Annex-Engineering/Carabiner-Docs/carabiner-distributor/images/Distributor_jstxh_2.png

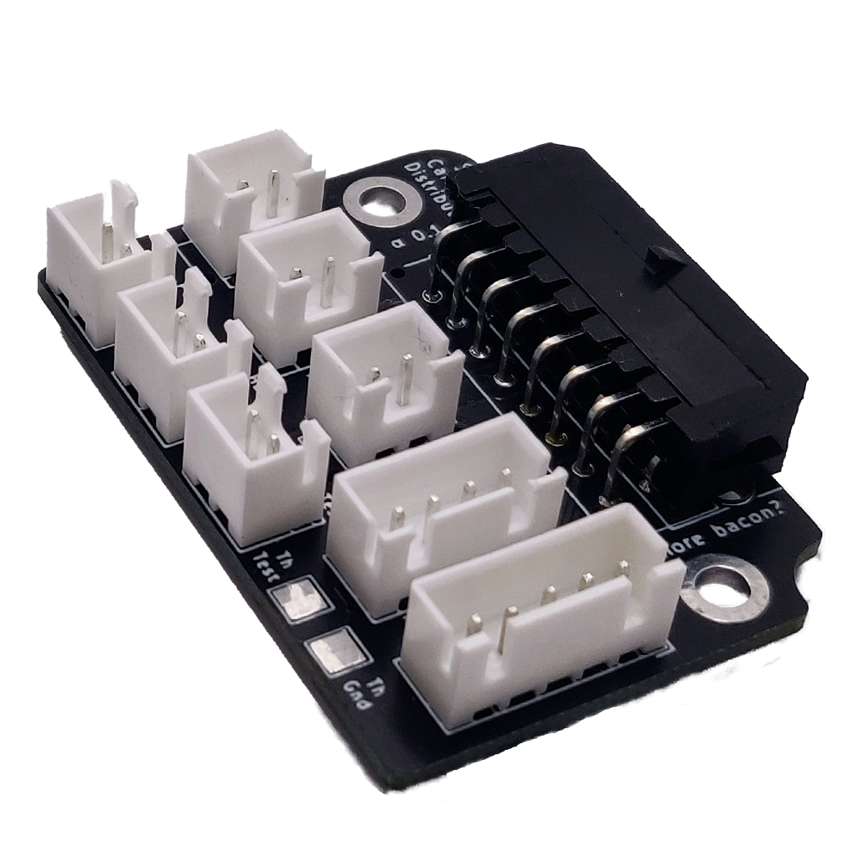
carabiner-distributor/images/Distributor_jstxh_2.png
