Annex-Engineering/Carabiner-Docs/carabiner-distributor/images/Distributor_microfit.png

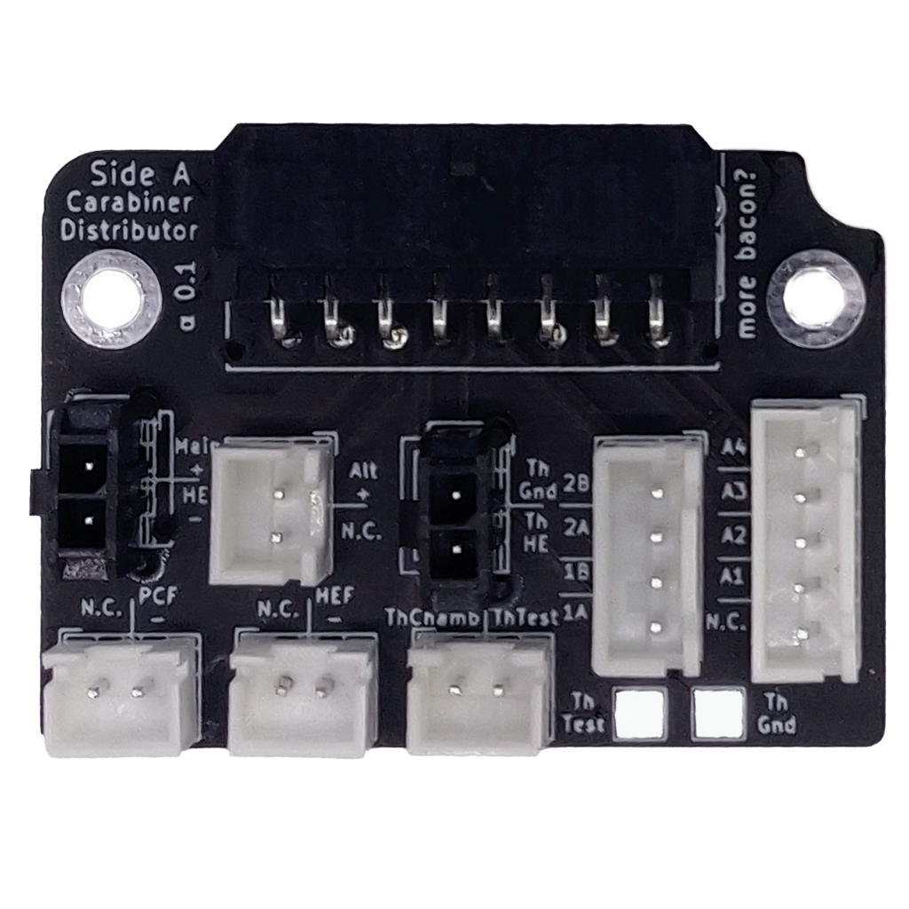
carabiner-distributor/images/Distributor_microfit.png
