Annex-Engineering/Carabiner-Docs/k3rabiner/images/Micro.jpg

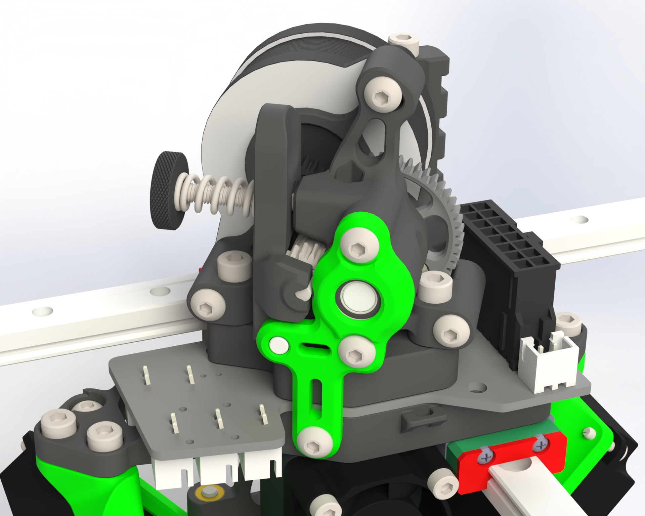
k3rabiner/images/Micro.jpg
