Annex-Engineering/Carabiner-Docs/k3rabiner/images/Mini 2.jpg

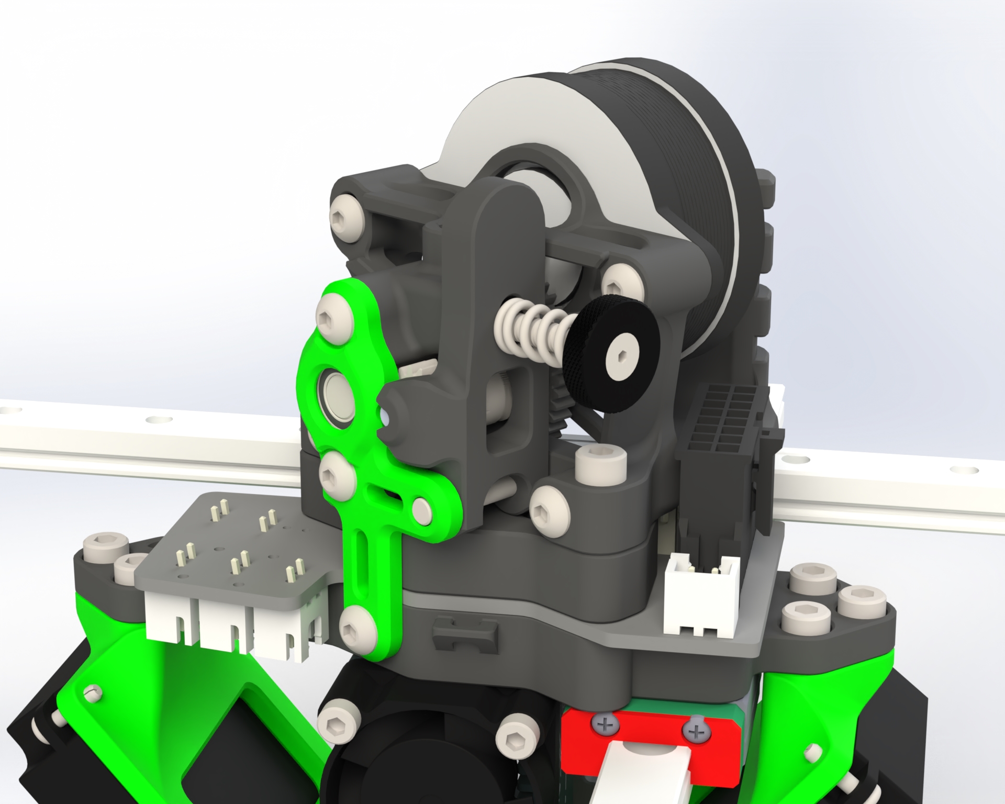
k3rabiner/images/Mini 2.jpg
