Annex-Engineering/Carabiner-Docs/k3rabiner/images/Mini.jpg

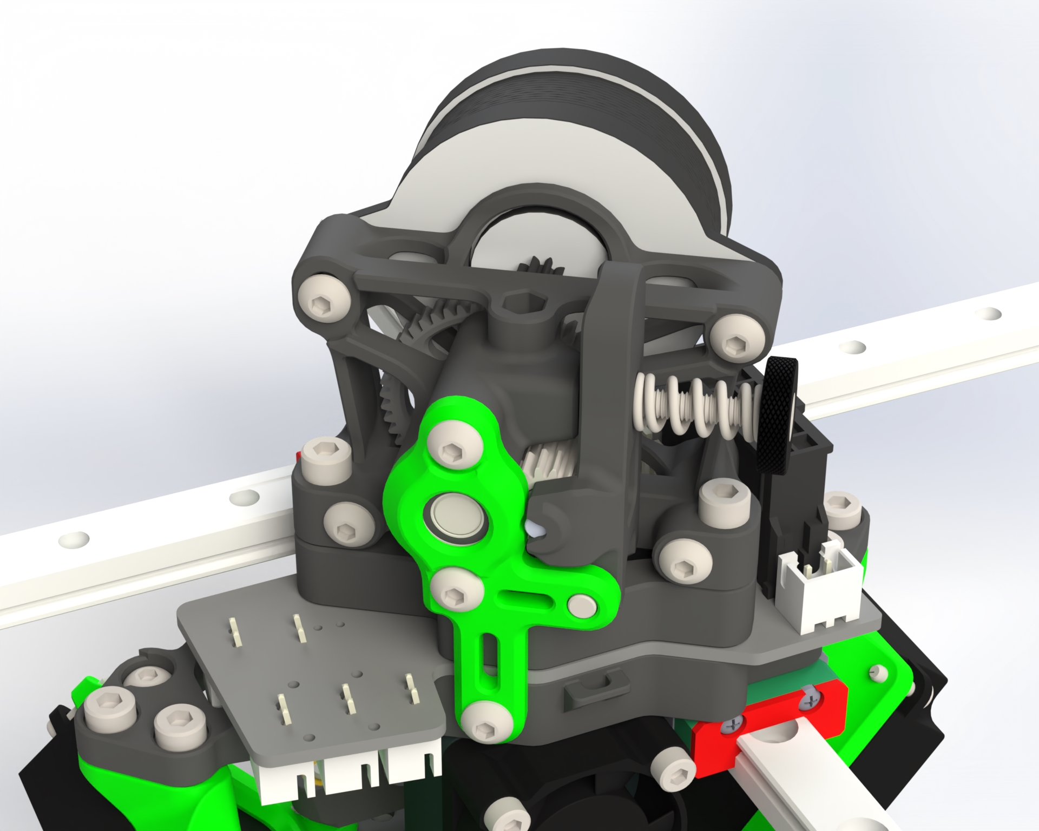
k3rabiner/images/Mini.jpg
