Annex-Engineering/Carabiner-Docs/k3rabiner/images/Untitled Project 41.jpg

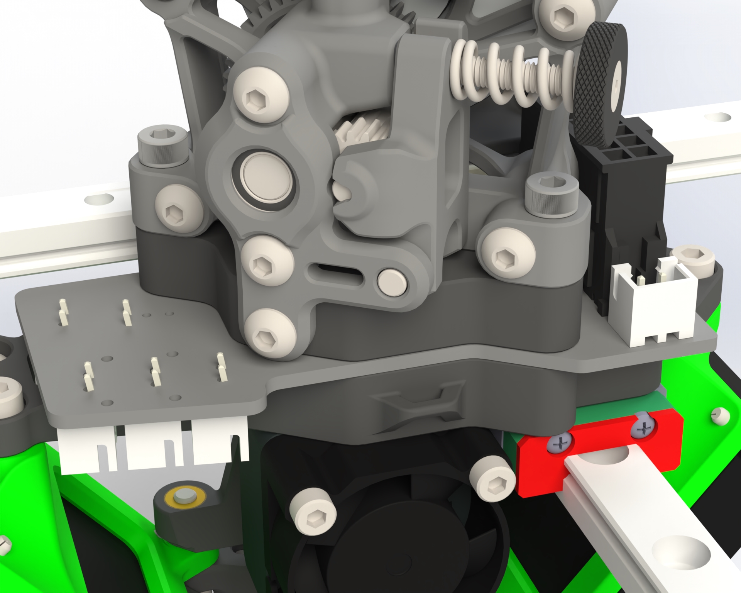
k3rabiner/images/Untitled Project 41.jpg
