Annex-Engineering/Carabiner-Docs/k3rabiner/Soldering_Jig_R1/k3rabiner-b_0_1_XH_Soldering_Jig.SLDPRT

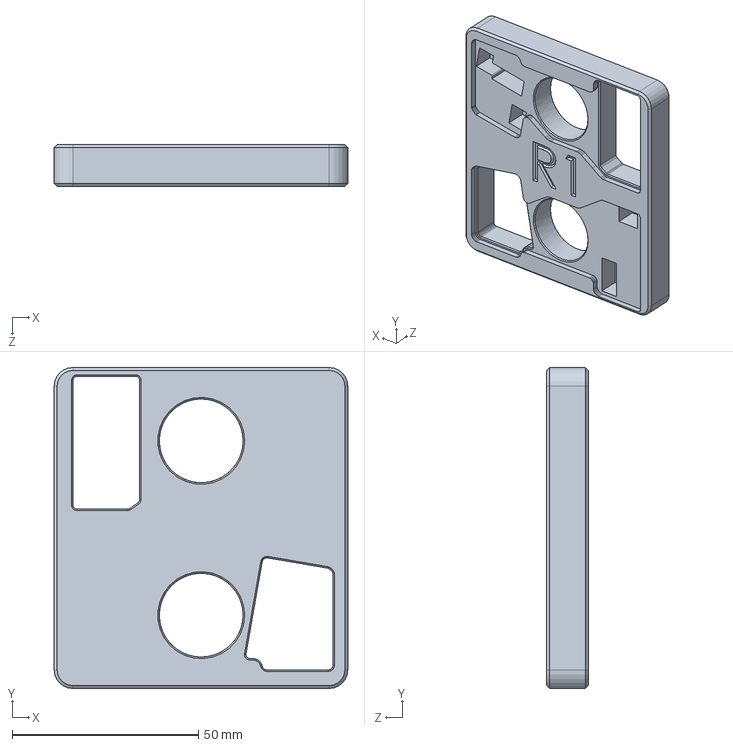
[picture p37: CAD file, 2024-07-17]
k3rabiner/Soldering_Jig_R1/k3rabiner-b_0_1_XH_Soldering_Jig.SLDPRT
78.8 x 86.1 x 11.3 mm
