Annex-Engineering/Carabiner-Docs/carabiner-classic/attachments/Afterburner/STLs/Clockwork_housing_x1_Rev1.STL

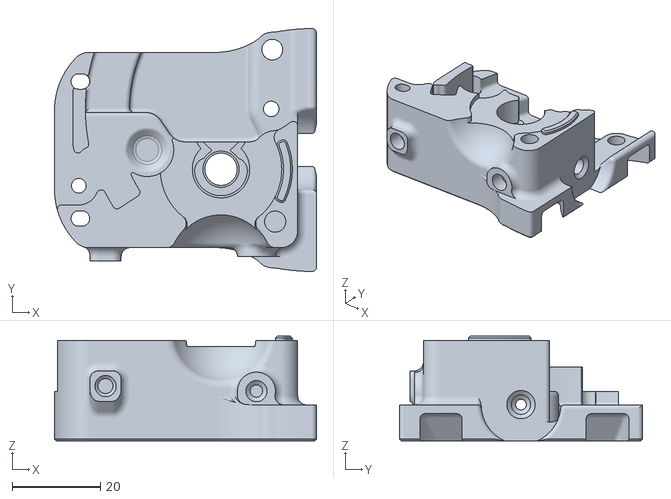
[picture p38: CAD file, 2024-07-17]
carabiner-classic/attachments/Afterburner/STLs/Clockwork_housing_x1_Rev1.STL
59.3 x 55.0 x 23.7
