Annex-Engineering/Carabiner-Docs/k3rabiner/Soldering_Jig_R1/k3rabiner-b_0_1-Jig_Bottom.SLDPRT

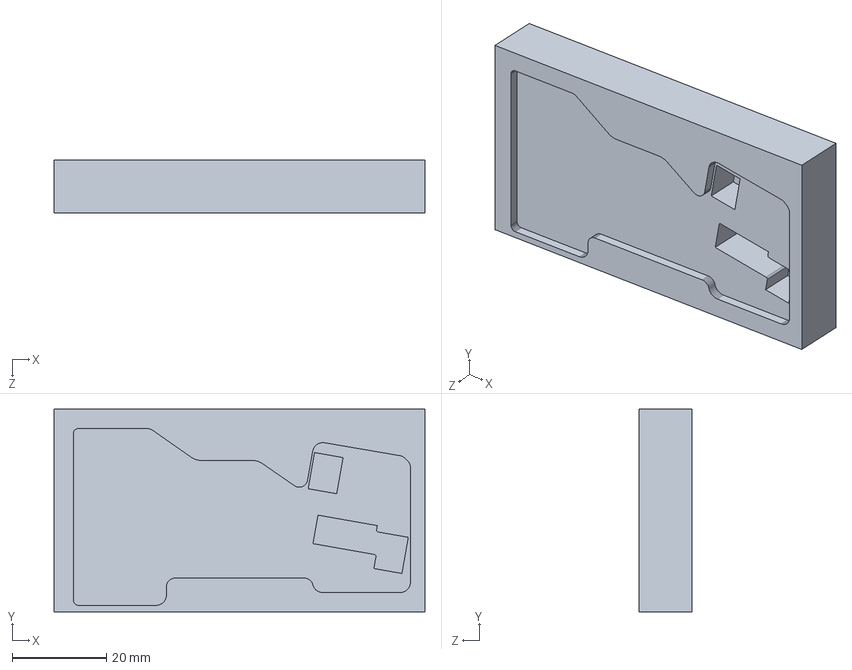
[picture p39: CAD file, 2024-07-17]
k3rabiner/Soldering_Jig_R1/k3rabiner-b_0_1-Jig_Bottom.SLDPRT
78.8 x 43.1 x 11.2 mm
